martin-wagner/adapter-9960/out/panel/stuff/VT9-PT/board_v1.png

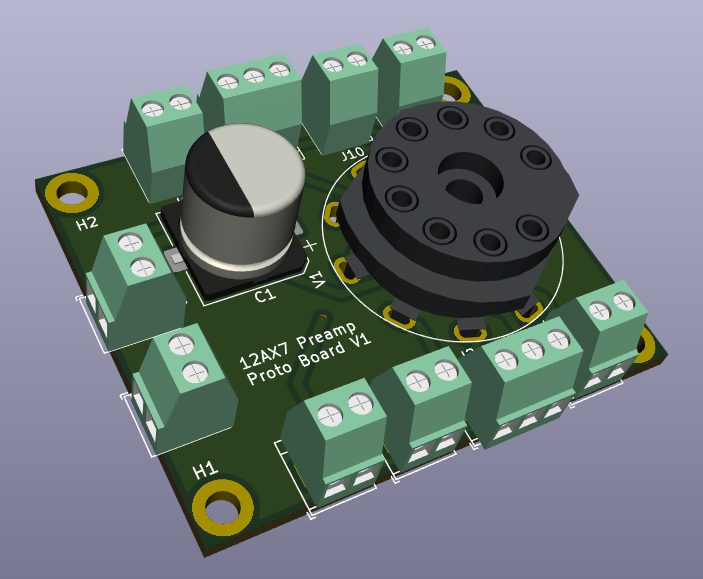
out/panel/stuff/VT9-PT/board_v1.png
