martin-wagner/adapter-9960/out/panel/stuff/VT9-PT/general_preamp.png

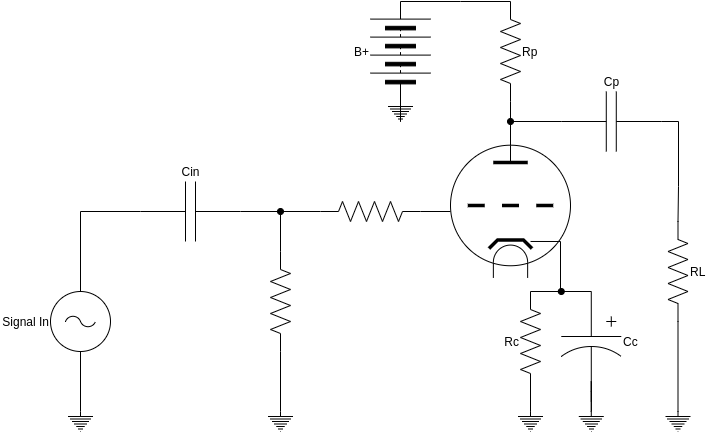
out/panel/stuff/VT9-PT/general_preamp.png
